tjipx71/Grupo10-Fundamentos-de-dise-o/Proyecto/ModuloElectrónico/Esquema revisión 1.0/Medidor-Q.kicad_sch

## KiCad design Proyecto/ModuloElectrónico/Esquema revisión 1.0/Medidor-Q.kicad_sch (2025-11-27)

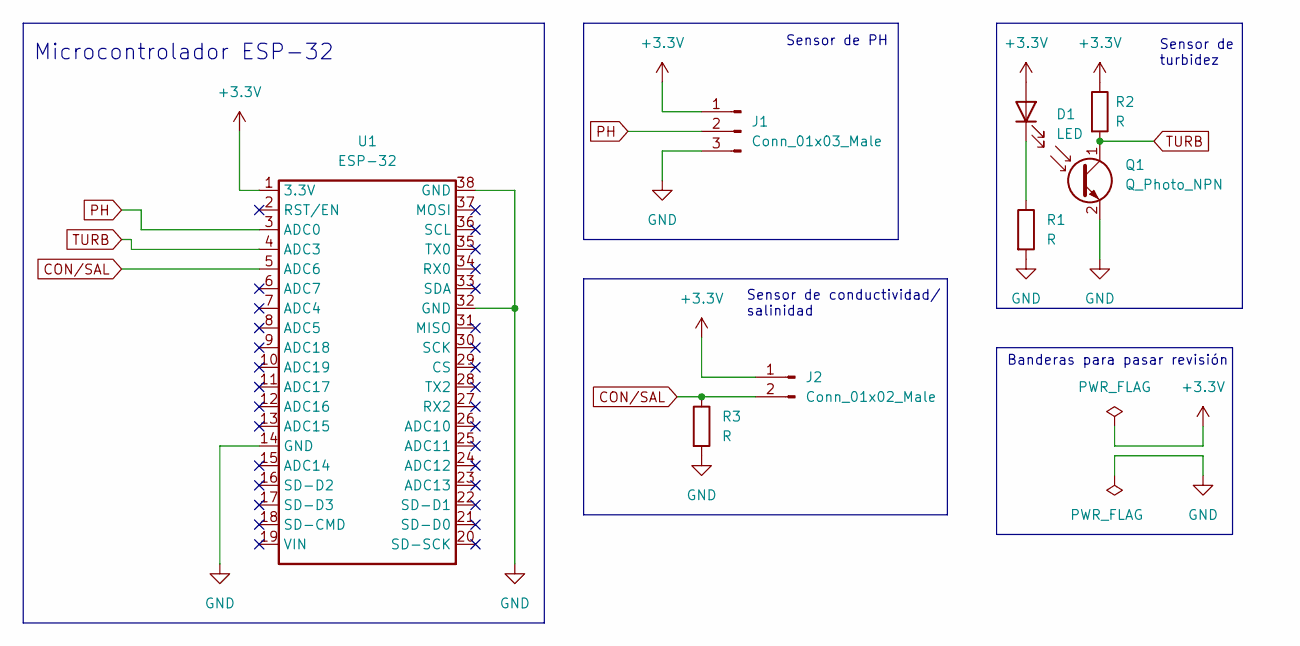
[picture p30: schematic Medidor-Q.kicad_sch]

Parts:
D1: LED
J1: Conn_01x03_Male
J2: Conn_01x02_Male
Q1: Q_Photo_NPN
R1, R2, R3: R
U1: ESP-32

Connections:
+3.3V: D1.2 (A), J1.1, J2.1, R2.1, U1.1 (3.3V)
CON/SAL: J2.2, R3.1, U1.5 (ADC6)
GND: J1.3, Q1.2 (E), R1.2, R3.2, U1.14 (GND), U1.32 (GND), U1.38 (GND)
unnamed: D1.1 (K), R1.1
PH: J1.2, U1.3 (ADC0)
TURB: Q1.1 (C), R2.2, U1.4 (ADC3)

Notes on the sheet:
Banderas para pasar revisión
Sensor de conductividad/ salinidad
Microcontrolador ESP-32
Sensor de PH
Sensor de turbidez
